jakkra/Gesture-Detecting-Macro-Keyboard/main/ble_hid.c

/* This example code is in the Public Domain (or CC0 licensed, at your option.)
   Unless required by applicable law or agreed to in writing, this software is
   distributed on an "AS IS" BASIS, WITHOUT WARRANTIES OR
   CONDITIONS OF ANY KIND, either express or implied.
*/

#include <stdio.h>
#include <stdlib.h>
#include <string.h>
#include "freertos/FreeRTOS.h"
#include "freertos/task.h"
#include "freertos/event_groups.h"
#include "esp_system.h"
#include "esp_wifi.h"
#include "esp_event.h"
#include "esp_log.h"
#include "nvs_flash.h"
#include "esp_bt.h"
#include "freertos/semphr.h"

#include "esp_hidd_prf_api.h"
#include "esp_bt_defs.h"
#include "esp_gap_ble_api.h"
#include "esp_gatts_api.h"
#include "esp_gatt_defs.h"
#include "esp_bt_main.h"
#include "esp_bt_device.h"
#include "driver/gpio.h"
#include "hid_dev.h"

#include "ble_hid.h"

#define TAG "BLE_HID"

#define HIDD_DEVICE_NAME            "GestureMacroKeyboard"
#define CHAR_DECLARATION_SIZE       (sizeof(uint8_t))

static uint16_t hid_conn_id = 0;
static bool sec_conn = false;
static xSemaphoreHandle sem_handle;
static hid_connection_callback* connection_callback;
static bool pairing_enabled = false;

static void hidd_event_callback(esp_hidd_cb_event_t event, esp_hidd_cb_param_t *param);

static uint8_t hidd_service_uuid128[] = {
    /* LSB <--------------------------------------------------------------------------------> MSB */
    //first uuid, 16bit, [12],[13] is the value
    0xfb, 0x34, 0x9b, 0x5f, 0x80, 0x00, 0x00, 0x80, 0x00, 0x10, 0x00, 0x00, 0x12, 0x18, 0x00, 0x00,
};

static esp_ble_adv_data_t hidd_adv_data = {
    .set_scan_rsp = false,
    .include_name = true,
    .include_txpower = true,
    .min_interval = 0x0006, //slave connection min interval, Time = min_interval * 1.25 msec
    .max_interval = 0x0010, //slave connection max interval, Time = max_interval * 1.25 msec
    .appearance = 0x03c0,       //HID Generic,
    .manufacturer_len = 0,
    .p_manufacturer_data =  NULL,
    .service_data_len = 0,
    .p_service_data = NULL,
    .service_uuid_len = sizeof(hidd_service_uuid128),
    .p_service_uuid = hidd_service_uuid128,
    .flag = 0x6,
};

static esp_ble_adv_params_t hidd_adv_params = {
    .adv_int_min        = 0x20,
    .adv_int_max        = 0x30,
    .adv_type           = ADV_TYPE_IND,
    .own_addr_type      = BLE_ADDR_TYPE_PUBLIC,
    //.peer_addr            =
    //.peer_addr_type       =
    .channel_map        = ADV_CHNL_ALL,
    .adv_filter_policy = ADV_FILTER_ALLOW_SCAN_ANY_CON_ANY,
};

static void hidd_event_callback(esp_hidd_cb_event_t event, esp_hidd_cb_param_t *param)
{
    switch(event) {
        case ESP_HIDD_EVENT_REG_FINISH: {
            if (param->init_finish.state == ESP_HIDD_INIT_OK) {
                //esp_bd_addr_t rand_addr = {0x04,0x11,0x11,0x11,0x11,0x05};
                esp_ble_gap_set_device_name(HIDD_DEVICE_NAME);
                esp_ble_gap_config_adv_data(&hidd_adv_data);

            }
            break;
        }
        case ESP_BAT_EVENT_REG: {
            break;
        }
        case ESP_HIDD_EVENT_DEINIT_FINISH:
	     break;
		case ESP_HIDD_EVENT_BLE_CONNECT: {
            ESP_LOGI(TAG, "ESP_HIDD_EVENT_BLE_CONNECT");
            hid_conn_id = param->connect.conn_id;
            connection_callback(BLE_HID_CONNECTED, &param->connect.remote_bda);
            break;
        }
        case ESP_HIDD_EVENT_BLE_DISCONNECT: {
            sec_conn = false;
            ESP_LOGI(TAG, "ESP_HIDD_EVENT_BLE_DISCONNECT");
            connection_callback(BLE_HID_DISCONNECTED, &param->disconnect.remote_bda);
            esp_ble_gap_start_advertising(&hidd_adv_params);
            break;
        }
        case ESP_HIDD_EVENT_BLE_VENDOR_REPORT_WRITE_EVT: {
            ESP_LOGI(TAG, "%s, ESP_HIDD_EVENT_BLE_VENDOR_REPORT_WRITE_EVT", __func__);
            ESP_LOG_BUFFER_HEX(TAG, param->vendor_write.data, param->vendor_write.length);
        }
        default:
            break;
    }
    return;
}

static void gap_event_handler(esp_gap_ble_cb_event_t event, esp_ble_gap_cb_param_t *param)
{
    switch (event) {
    case ESP_GAP_BLE_PASSKEY_REQ_EVT:
        esp_ble_passkey_reply(param->ble_security.ble_req.bd_addr, false, 0x00);
        break;
    case ESP_GAP_BLE_ADV_DATA_SET_COMPLETE_EVT:
        esp_ble_gap_start_advertising(&hidd_adv_params);
        break;
     case ESP_GAP_BLE_SEC_REQ_EVT:
        for(int i = 0; i < ESP_BD_ADDR_LEN; i++) {
             ESP_LOGD(TAG, "%x:",param->ble_security.ble_req.bd_addr[i]);
        }
        if (pairing_enabled) {
            esp_ble_gap_security_rsp(param->ble_security.ble_req.bd_addr, true);
        } else {
            esp_ble_gap_security_rsp(param->ble_security.ble_req.bd_addr, false);
        }
	    break;
     case ESP_GAP_BLE_AUTH_CMPL_EVT:
        sec_conn = true;
        esp_bd_addr_t bd_addr;
        memcpy(bd_addr, param->ble_security.auth_cmpl.bd_addr, sizeof(esp_bd_addr_t));
        ESP_LOGI(TAG, "remote BD_ADDR: %08x%04x",\
                (bd_addr[0] << 24) + (bd_addr[1] << 16) + (bd_addr[2] << 8) + bd_addr[3],
                (bd_addr[4] << 8) + bd_addr[5]);
        ESP_LOGI(TAG, "address type = %d", param->ble_security.auth_cmpl.addr_type);
        ESP_LOGI(TAG, "pair status = %s",param->ble_security.auth_cmpl.success ? "success" : "fail");
        if (!param->ble_security.auth_cmpl.success) {
            ESP_LOGE(TAG, "fail reason = 0x%x",param->ble_security.auth_cmpl.fail_reason);
            connection_callback(BLE_HID_BOND_FAILED, &param->ble_security.auth_cmpl.bd_addr);
        } else {
            connection_callback(BLE_HID_BOND_SUCCESS, &param->ble_security.auth_cmpl.bd_addr);
        }
        ble_hid_set_pairable(false);
        break;
    default:
        break;
    }
}

void ble_hid_init(hid_connection_callback* callback) {
    esp_err_t ret;

    ESP_ERROR_CHECK(esp_bt_controller_mem_release(ESP_BT_MODE_CLASSIC_BT));

    esp_bt_controller_config_t bt_cfg = BT_CONTROLLER_INIT_CONFIG_DEFAULT();
    ret = esp_bt_controller_init(&bt_cfg);
    if (ret) {
        ESP_LOGE(TAG, "%s initialize controller failed\n", __func__);
        return;
    }

    ret = esp_bt_controller_enable(ESP_BT_MODE_BLE);
    if (ret) {
        ESP_LOGE(TAG, "%s enable controller failed\n", __func__);
        return;
    }

    ret = esp_bluedroid_init();
    if (ret) {
        ESP_LOGE(TAG, "%s init bluedroid failed\n", __func__);
        return;
    }

    ret = esp_bluedroid_enable();
    if (ret) {
        ESP_LOGE(TAG, "%s init bluedroid failed\n", __func__);
        return;
    }

    if((ret = esp_hidd_profile_init()) != ESP_OK) {
        ESP_LOGE(TAG, "%s init bluedroid failed\n", __func__);
    }

    esp_ble_gap_register_callback(gap_event_handler);
    esp_hidd_register_callbacks(hidd_event_callback);

    // Secure Connections only.
    esp_ble_auth_req_t auth_req = ESP_LE_AUTH_BOND | ESP_LE_AUTH_REQ_SC_ONLY | ESP_BLE_ONLY_ACCEPT_SPECIFIED_AUTH_ENABLE;
    esp_ble_io_cap_t iocap = ESP_IO_CAP_IN;
    uint8_t key_size = 16;
    uint8_t init_key = ESP_BLE_ENC_KEY_MASK | ESP_BLE_ID_KEY_MASK;
    uint8_t rsp_key = ESP_BLE_ENC_KEY_MASK | ESP_BLE_ID_KEY_MASK;
    esp_ble_gap_set_security_param(ESP_BLE_SM_AUTHEN_REQ_MODE, &auth_req, sizeof(uint8_t));
    esp_ble_gap_set_security_param(ESP_BLE_SM_IOCAP_MODE, &iocap, sizeof(uint8_t));
    esp_ble_gap_set_security_param(ESP_BLE_SM_MAX_KEY_SIZE, &key_size, sizeof(uint8_t));
    esp_ble_gap_set_security_param(ESP_BLE_SM_SET_INIT_KEY, &init_key, sizeof(uint8_t));
    esp_ble_gap_set_security_param(ESP_BLE_SM_SET_RSP_KEY, &rsp_key, sizeof(uint8_t));

    connection_callback = callback;

    sem_handle = xSemaphoreCreateBinary();
    assert(sem_handle != NULL);
    xSemaphoreGive(sem_handle);
}

esp_err_t ble_hid_send_key(key_mask_t key_mask, uint8_t* keys, uint16_t num_keys)
{
    esp_err_t ret = ESP_FAIL;

    if (sec_conn) {
        if (uxSemaphoreGetCount(sem_handle) == 0) {
            esp_hidd_send_keyboard_value(hid_conn_id, key_mask, keys, num_keys);
            ret = ESP_OK;
        } else {
            ret = ESP_FAIL;
        }
    }

    return ret;
}

esp_err_t ble_hid_send_consumer_key(consumer_cmd_t key, bool key_pressed)
{
    esp_err_t ret = ESP_FAIL;

    if (sec_conn) {
        if (uxSemaphoreGetCount(sem_handle) == 0) {
            esp_hidd_send_consumer_value(hid_conn_id, key, key_pressed);
            ret = ESP_OK;
        } else {
            ret = ESP_FAIL;
        }
    }

    return ret;
}

void ble_hid_set_pairable(bool pairable)
{
    esp_ble_io_cap_t iocap;
    pairing_enabled = pairable;
    if (pairable) {
        iocap = ESP_IO_CAP_NONE;
    } else {
        iocap = ESP_IO_CAP_IN;
    }
    // A bit hacky, but cannot find any other way to have pairing enabled by a button.
    // Doing it by using whitelisting (adv_filter_policy) does not work and no way to enable/disable pairing.
    // When pairing is disabled, set IOCAP to keyboard and just reject the passkey request.
    esp_ble_gap_set_security_param(ESP_BLE_SM_IOCAP_MODE, &iocap, sizeof(uint8_t));
}

esp_err_t ble_hid_request_access(uint32_t timeout_ms) {
    if (xSemaphoreTake(sem_handle, pdMS_TO_TICKS(timeout_ms)) == pdPASS) {
        return ESP_OK;
    }

    return ESP_ERR_TIMEOUT;
}

// Should provide a handle also so that you cannot leave access for someone else, but this will do for now.
esp_err_t ble_hid_give_access(void) {
    if (uxSemaphoreGetCount(sem_handle) != 0) {
        // 
        return ESP_FAIL;
    }
    xSemaphoreGive(sem_handle);
    
    return ESP_OK;
}
