jakkra/Gesture-Detecting-Macro-Keyboard/main/gesture_model_tflite.cc

#include "gesture_model_tflite.h"
const unsigned char gesture_model_tflite_data[] = {
  0x1c, 0x00, 0x00, 0x00, 0x54, 0x46, 0x4c, 0x33, 0x14, 0x00, 0x20, 0x00,
  0x04, 0x00, 0x08, 0x00, 0x0c, 0x00, 0x10, 0x00, 0x14, 0x00, 0x00, 0x00,
  0x18, 0x00, 0x1c, 0x00, 0x14, 0x00, 0x00, 0x00, 0x03, 0x00, 0x00, 0x00,
  0x18, 0x00, 0x00, 0x00, 0x2c, 0x00, 0x00, 0x00, 0xe4, 0x00, 0x00, 0x00,
  0x2c, 0x00, 0x00, 0x00, 0x8c, 0x00, 0x00, 0x00, 0x84, 0x00, 0x00, 0x00,
  0x05, 0x00, 0x00, 0x00, 0x5c, 0x08, 0x00, 0x00, 0x78, 0x07, 0x00, 0x00,
  0xc8, 0x03, 0x00, 0x00, 0x04, 0x03, 0x00, 0x00, 0xc8, 0x01, 0x00, 0x00,
  0x01, 0x00, 0x00, 0x00, 0xdc, 0x00, 0x00, 0x00, 0x17, 0x00, 0x00, 0x00,
  0x70, 0x87, 0x00, 0x00, 0x6c, 0x87, 0x00, 0x00, 0x6c, 0x86, 0x00, 0x00,
  0xb8, 0x85, 0x00, 0x00, 0x10, 0x85, 0x00, 0x00, 0x68, 0x84, 0x00, 0x00,
  0xe4, 0x83, 0x00, 0x00, 0x78, 0x83, 0x00, 0x00, 0x28, 0x43, 0x00, 0x00,
  0x14, 0x41, 0x00, 0x00, 0x98, 0x3f, 0x00, 0x00, 0x3c, 0x2d, 0x00, 0x00,
  0xe0, 0x08, 0x00, 0x00, 0x3c, 0x87, 0x00, 0x00, 0x38, 0x87, 0x00, 0x00,
  0x34, 0x87, 0x00, 0x00, 0x30, 0x87, 0x00, 0x00, 0x2c, 0x87, 0x00, 0x00,
  0x28, 0x87, 0x00, 0x00, 0x24, 0x87, 0x00, 0x00, 0x20, 0x87, 0x00, 0x00,
  0x1c, 0x87, 0x00, 0x00, 0x3c, 0x00, 0x00, 0x00, 0x00, 0x00, 0x00, 0x00,
  0x01, 0x00, 0x00, 0x00, 0x0c, 0x00, 0x00, 0x00, 0x08, 0x00, 0x0c, 0x00,
  0x04, 0x00, 0x08, 0x00, 0x08, 0x00, 0x00, 0x00, 0x08, 0x00, 0x00, 0x00,
  0x16, 0x00, 0x00, 0x00, 0x13, 0x00, 0x00, 0x00, 0x6d, 0x69, 0x6e, 0x5f,
  0x72, 0x75, 0x6e, 0x74, 0x69, 0x6d, 0x65, 0x5f, 0x76, 0x65, 0x72, 0x73,
  0x69, 0x6f, 0x6e, 0x00, 0x26, 0x7a, 0xff, 0xff, 0x04, 0x00, 0x00, 0x00,
  0x10, 0x00, 0x00, 0x00, 0x31, 0x2e, 0x35, 0x2e, 0x30, 0x00, 0x00, 0x00,
  0x00, 0x00, 0x00, 0x00, 0x00, 0x00, 0x00, 0x00, 0x0f, 0x00, 0x00, 0x00,
  0x4d, 0x4c, 0x49, 0x52, 0x20, 0x43, 0x6f, 0x6e, 0x76, 0x65, 0x72, 0x74,
  0x65, 0x64, 0x2e, 0x00, 0x00, 0x00, 0x0e, 0x00, 0x18, 0x00, 0x04, 0x00,
  0x08, 0x00, 0x0c, 0x00, 0x10, 0x00, 0x14, 0x00, 0x0e, 0x00, 0x00, 0x00,
  0x14, 0x00, 0x00, 0x00, 0x68, 0x00, 0x00, 0x00, 0x6c, 0x00, 0x00, 0x00,
  0x70, 0x00, 0x00, 0x00, 0x94, 0x00, 0x00, 0x00, 0x15, 0x00, 0x00, 0x00,
  0x2c, 0x86, 0x00, 0x00, 0xbc, 0x85, 0x00, 0x00, 0x18, 0x85, 0x00, 0x00,
  0x70, 0x84, 0x00, 0x00, 0xc8, 0x83, 0x00, 0x00, 0x20, 0x83, 0x00, 0x00,
  0xb0, 0x82, 0x00, 0x00, 0x48, 0x82, 0x00, 0x00, 0xf4, 0x41, 0x00, 0x00,
  0xd8, 0x3f, 0x00, 0x00, 0x5c, 0x3e, 0x00, 0x00, 0x00, 0x2c, 0x00, 0x00,
  0x2c, 0x07, 0x00, 0x00, 0x48, 0x06, 0x00, 0x00, 0xec, 0x04, 0x00, 0x00,
  0xe0, 0x03, 0x00, 0x00, 0x34, 0x03, 0x00, 0x00, 0x8c, 0x02, 0x00, 0x00,
  0xc8, 0x01, 0x00, 0x00, 0x04, 0x01, 0x00, 0x00, 0x88, 0x00, 0x00, 0x00,
  0x01, 0x00, 0x00, 0x00, 0x00, 0x00, 0x00, 0x00, 0x01, 0x00, 0x00, 0x00,
  0x14, 0x00, 0x00, 0x00, 0x09, 0x00, 0x00, 0x00, 0x90, 0x06, 0x00, 0x00,
  0xb0, 0x05, 0x00, 0x00, 0x78, 0x04, 0x00, 0x00, 0x6c, 0x03, 0x00, 0x00,
  0xbc, 0x02, 0x00, 0x00, 0x20, 0x02, 0x00, 0x00, 0x40, 0x01, 0x00, 0x00,
  0x98, 0x00, 0x00, 0x00, 0x10, 0x00, 0x00, 0x00, 0x04, 0x00, 0x00, 0x00,
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
};
unsigned int D__trill_training_output__gesture_model_tflite_len = 34772;
